Pongkemon01/ServoCoordinator/Software/nuttx/Documentation/NuttX320.png

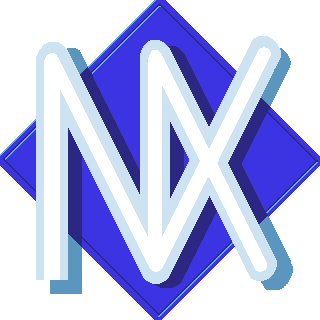
Software/nuttx/Documentation/NuttX320.png
