Pongkemon01/ServoCoordinator/Software/nuttx/Documentation/NuttXScreenShot.jpg

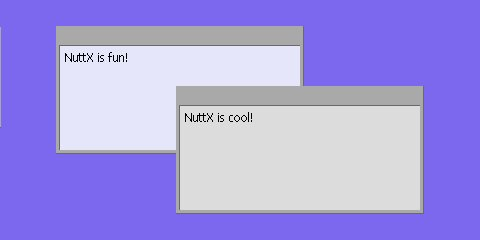
Software/nuttx/Documentation/NuttXScreenShot.jpg
