Pongkemon01/ServoCoordinator/Software/nuttx/Documentation/NXOrganization.gif

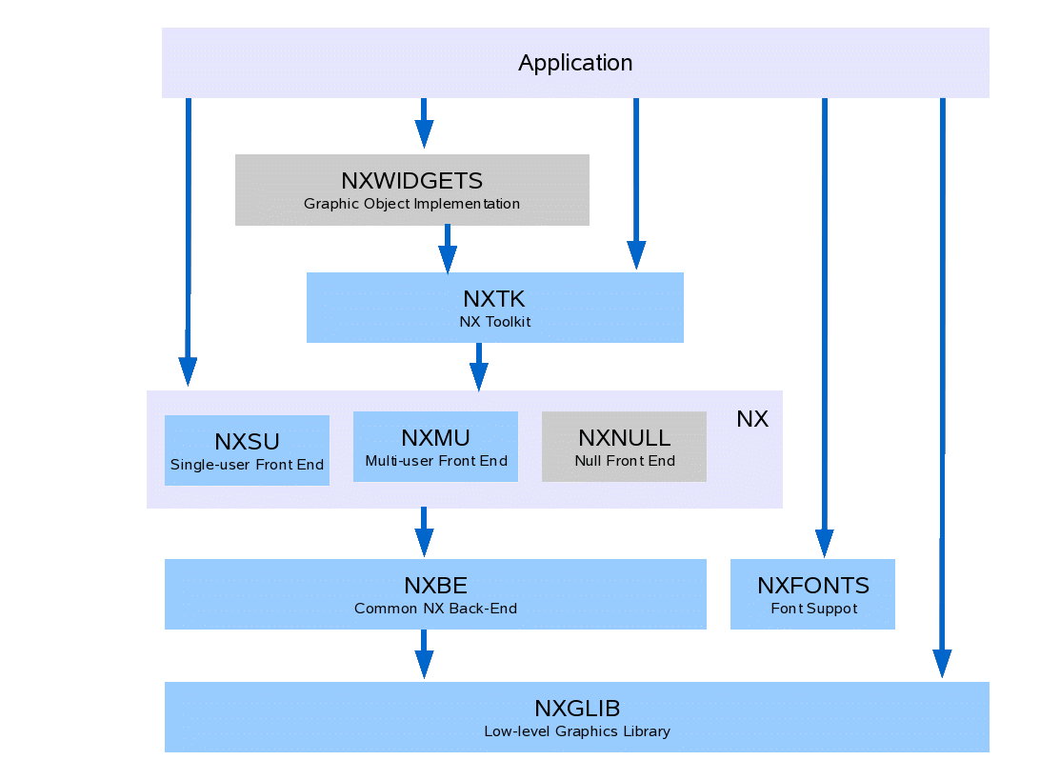
Software/nuttx/Documentation/NXOrganization.gif
