Pongkemon01/ServoCoordinator/Software/nuttx/Documentation/pm.png

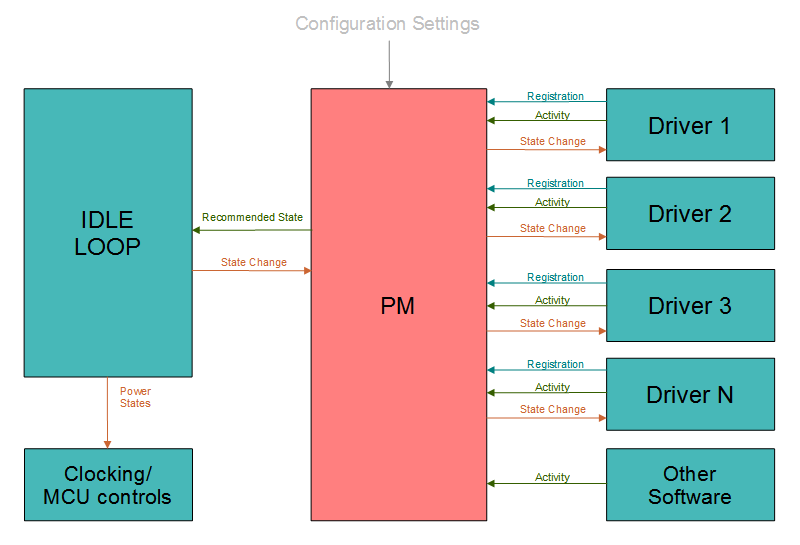
Software/nuttx/Documentation/pm.png
