Pongkemon01/ServoCoordinator/Software/apps/graphics/nxwidgets/UnitTests/CButton/cbutton-pushed.png

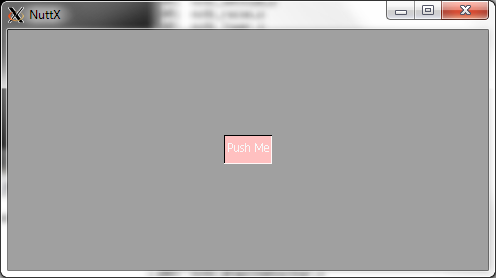
Software/apps/graphics/nxwidgets/UnitTests/CButton/cbutton-pushed.png
