Pongkemon01/ServoCoordinator/Software/apps/graphics/nxwidgets/UnitTests/CButton/cbutton-released.png

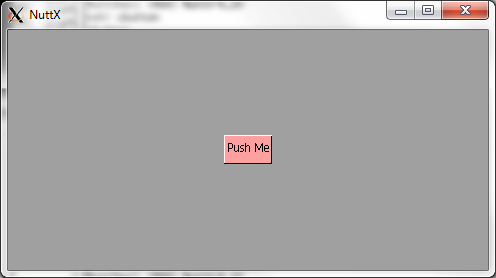
Software/apps/graphics/nxwidgets/UnitTests/CButton/cbutton-released.png
