Pongkemon01/ServoCoordinator/Software/apps/graphics/nxwidgets/UnitTests/CButtonArray/cbuttonarray.png

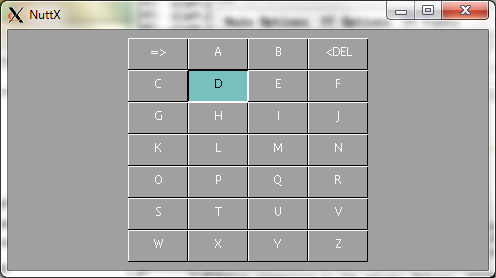
Software/apps/graphics/nxwidgets/UnitTests/CButtonArray/cbuttonarray.png
