Pongkemon01/ServoCoordinator/Software/apps/graphics/nxwidgets/UnitTests/CCheckBox/ccheckbox.png

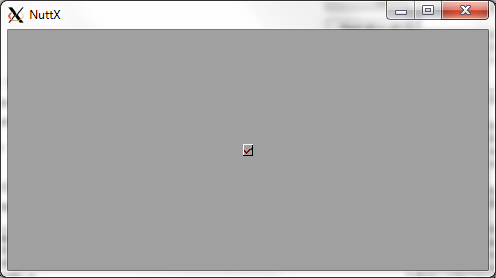
Software/apps/graphics/nxwidgets/UnitTests/CCheckBox/ccheckbox.png
