Pongkemon01/ServoCoordinator/Software/apps/graphics/nxwidgets/UnitTests/CLabel/clabel.png

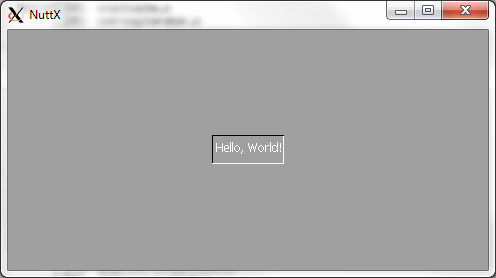
Software/apps/graphics/nxwidgets/UnitTests/CLabel/clabel.png
