Pongkemon01/ServoCoordinator/Software/apps/graphics/nxwidgets/UnitTests/CProgressBar/cprogressbar.png

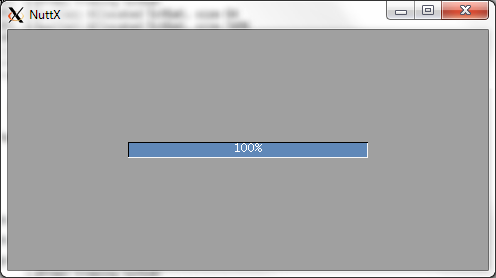
Software/apps/graphics/nxwidgets/UnitTests/CProgressBar/cprogressbar.png
