Pongkemon01/ServoCoordinator/Software/apps/graphics/nxwidgets/UnitTests/CRadioButton/cradiobutton.png

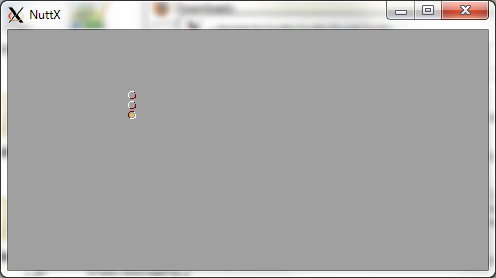
Software/apps/graphics/nxwidgets/UnitTests/CRadioButton/cradiobutton.png
