Pongkemon01/ServoCoordinator/Software/apps/graphics/nxwidgets/UnitTests/CScrollbarHorizontal/cscrollbarhorizontal.png

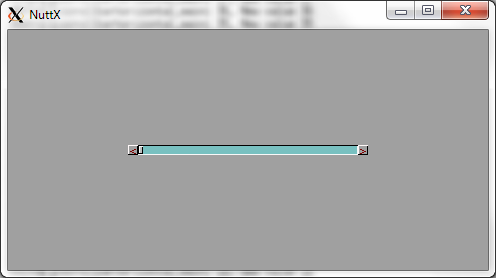
Software/apps/graphics/nxwidgets/UnitTests/CScrollbarHorizontal/cscrollbarhorizontal.png
