Pongkemon01/ServoCoordinator/Software/apps/graphics/nxwidgets/UnitTests/CScrollbarVertical/cscrollbarvertical.png

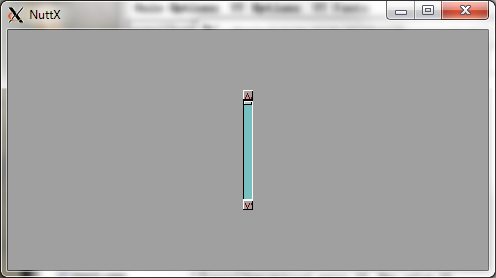
Software/apps/graphics/nxwidgets/UnitTests/CScrollbarVertical/cscrollbarvertical.png
