Pongkemon01/ServoCoordinator/Software/apps/graphics/nxwidgets/UnitTests/CSliderHorizonal/csliderhorizontal.png

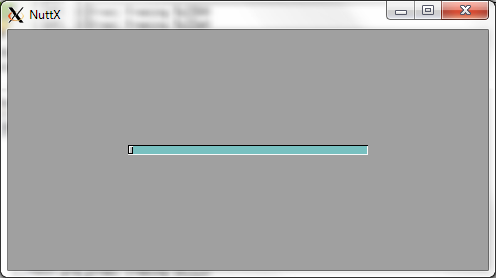
Software/apps/graphics/nxwidgets/UnitTests/CSliderHorizonal/csliderhorizontal.png
