Pongkemon01/ServoCoordinator/Software/apps/graphics/nxwidgets/UnitTests/CSliderVertical/cslidervertical.png

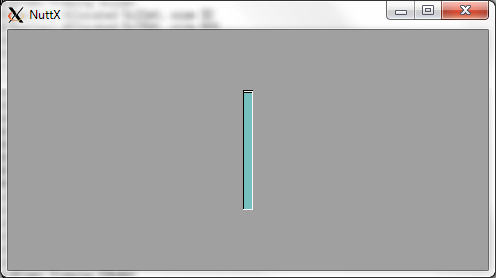
Software/apps/graphics/nxwidgets/UnitTests/CSliderVertical/cslidervertical.png
