Pongkemon01/ServoCoordinator/Software/apps/graphics/nxwidgets/UnitTests/CTextBox/ctextbox.png

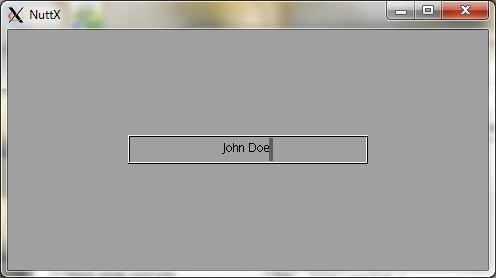
Software/apps/graphics/nxwidgets/UnitTests/CTextBox/ctextbox.png
