Pongkemon01/ServoCoordinator/Software/nuttx/arch/arm/src/kl/kl_gpio.h

/****************************************************************************
 * arch/arm/src/kl/kl_gpio.h
 *
 *   Copyright (C) 2013 Gregory Nutt. All rights reserved.
 *   Author: Gregory Nutt <gnutt@nuttx.org>
 *
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
 * 1. Redistributions of source code must retain the above copyright
 *    notice, this list of conditions and the following disclaimer.
 * 2. Redistributions in binary form must reproduce the above copyright
 *    notice, this list of conditions and the following disclaimer in
 *    the documentation and/or other materials provided with the
 *    distribution.
 * 3. Neither the name NuttX nor the names of its contributors may be
 *    used to endorse or promote products derived from this software
 *    without specific prior written permission.
 *
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
 ****************************************************************************/

#ifndef __ARCH_ARM_SRC_KL_KINETIS_GPIO_H
#define __ARCH_ARM_SRC_KL_KINETIS_GPIO_H

/****************************************************************************
 * Included Files
 ****************************************************************************/

#include <nuttx/config.h>

#include <stdbool.h>

#include <nuttx/irq.h>

#include "kl_config.h"
#include "hardware/kl_gpio.h"
#include "hardware/kl_port.h"

/****************************************************************************
 * Pre-processor Declarations
 ****************************************************************************/
/* Bit-encoded input to kl_pinconfig() *****************************************/
/* General form (32-bits, only 22 bits are unused in the encoding):
 *
 * oooo mmmv iiii ifd- ---- -ppp ---b bbbb
 */

/* Bits 25-31: 7 bits are used to encode the basic pin configuration:
 *
 * oooo mmm- ---- ---- ---- ---- ---- ----
 * |    `--- mmm: mode
 * `------- oooo: options (may be combined)
 */

#define _PIN_MODE_SHIFT        (25)                    /* Bits 25-27: Pin mode */
#define _PIN_MODE_MASK         (7 << _PIN_MODE_SHIFT)
#define _PIN_OPTIONS_SHIFT     (28)                    /* Bits 28-31: Pin mode options */
#define _PIN_OPTIONS_MASK      (15 << _PIN_OPTIONS_SHIFT)

/* Port Modes */

#define PIN_MODE_ANALOG        (0)                     /* 000 Pin Disabled (Analog) */
#define PIN_MODE_GPIO          (1)                     /* 001 Alternative 1 (GPIO) */
#define PIN_MODE_ALT2          (2)                     /* 010 Alternative 2 */
#define PIN_MODE_ALT3          (3)                     /* 011 Alternative 3 */
#define PIN_MODE_ALT4          (4)                     /* 100 Alternative 4 */
#define PIN_MODE_ALT5          (5)                     /* 101 Alternative 5 */
#define PIN_MODE_ALT6          (6)                     /* 110 Alternative 6 */
#define PIN_MODE_ALT7          (7)                     /* 111 Alternative 7 */

#define _PIN_MODE_ANALOG       (0 << _PIN_MODE_SHIFT)  /* 000 Pin Disabled (Analog) */
#define _PIN_MODE_GPIO         (1 << _PIN_MODE_SHIFT)  /* 001 Alternative 1 (GPIO) */
#define _PIN_MODE_ALT2         (2 << _PIN_MODE_SHIFT)  /* 010 Alternative 2 */
#define _PIN_MODE_ALT3         (3 << _PIN_MODE_SHIFT)  /* 011 Alternative 3 */
#define _PIN_MODE_ALT4         (4 << _PIN_MODE_SHIFT)  /* 100 Alternative 4 */
#define _PIN_MODE_ALT5         (5 << _PIN_MODE_SHIFT)  /* 101 Alternative 5 */
#define _PIN_MODE_ALT6         (6 << _PIN_MODE_SHIFT)  /* 110 Alternative 6 */
#define _PIN_MODE_ALT7         (7 << _PIN_MODE_SHIFT)  /* 111 Alternative 7 */

/* Options for all digital modes (Alternatives 1-7).  None of the digital
 * options apply if the analog mode is selected.
 */

#define _PIN_IO_MASK           (1 << _PIN_OPTIONS_SHIFT) /* xxx1 Digital input/output mask */
#define _PIN_INPUT             (0 << _PIN_OPTIONS_SHIFT) /* xxx0 Digital input */
#define _PIN_OUTPUT            (1 << _PIN_OPTIONS_SHIFT) /* xxx1 Digital output */

#define _PIN_INPUT_PULLMASK    (7 << _PIN_OPTIONS_SHIFT) /* x111 Mask for pull-up or -down bits */
#define _PIN_INPUT_PULLDOWN    (2 << _PIN_OPTIONS_SHIFT) /* x010 Input with internal pull-down resistor */
#define _PIN_INPUT_PULLUP      (6 << _PIN_OPTIONS_SHIFT) /* x110 Input with internal pull-up resistor */

#define _PIN_OUTPUT_SLEW_MASK  (3 << _PIN_OPTIONS_SHIFT) /* xx11 Mask to test for slow slew rate */
#define _PIN_OUTPUT_FAST       (1 << _PIN_OPTIONS_SHIFT) /* xx01 Output with fast slew rate */
#define _PIN_OUTPUT_SLOW       (3 << _PIN_OPTIONS_SHIFT) /* xx11 Output with slow slew rate */
#define _PIN_OUTPUT_OD_MASK    (5 << _PIN_OPTIONS_SHIFT) /* x1x1 Mask to test for open drain */
#define _PIN_OUTPUT_OPENDRAIN  (5 << _PIN_OPTIONS_SHIFT) /* x1x1 Output with open drain enabled */
#define _PIN_OUTPUT_DRIVE_MASK (9 << _PIN_OPTIONS_SHIFT) /* 1xx1 Mask to test for high drive strengh */
#define _PIN_OUTPUT_LOWDRIVE   (1 << _PIN_OPTIONS_SHIFT) /* 0xx1 Output with low drive strength */
#define _PIN_OUTPUT_HIGHDRIVE  (9 << _PIN_OPTIONS_SHIFT) /* 1xx1 Output with high drive strength */

/* End-user pin modes and configurations.  Notes:  (1) None of the digital options
 * are available for the analog mode, (2) digital settings may be combined (OR'ed)
 * provided that input-only and output-only options are not intermixed.
 */

#define PIN_ANALOG             _PIN_MODE_ANALOG

#define GPIO_INPUT             (_PIN_MODE_GPIO | _PIN_INPUT)
#define GPIO_PULLDOWN          (_PIN_MODE_GPIO | _PIN_INPUT_PULLDOWN)
#define GPIO_PULLUP            (_PIN_MODE_GPIO | _PIN_INPUT_PULLUP)
#define GPIO_OUTPUT            (_PIN_MODE_GPIO | _PIN_OUTPUT)
#define GPIO_FAST              (_PIN_MODE_GPIO | _PIN_OUTPUT_FAST)
#define GPIO_SLOW              (_PIN_MODE_GPIO | _PIN_OUTPUT_SLOW)
#define GPIO_OPENDRAIN         (_PIN_MODE_GPIO | _PIN_OUTPUT_LOWDRIVE)
#define GPIO_LOWDRIVE          (_PIN_MODE_GPIO | _PIN_OUTPUT_OPENDRAIN)
#define GPIO_HIGHDRIVE         (_PIN_MODE_GPIO | _PIN_OUTPUT_HIGHDRIVE)

#define PIN_ALT2               _PIN_MODE_ALT2
#define PIN_ALT2_INPUT         (_PIN_MODE_ALT2 | _PIN_INPUT)
#define PIN_ALT2_PULLDOWN      (_PIN_MODE_ALT2 | _PIN_INPUT_PULLDOWN)
#define PIN_ALT2_PULLUP        (_PIN_MODE_ALT2 | _PIN_INPUT_PULLUP)
#define PIN_ALT2_OUTPUT        (_PIN_MODE_ALT2 | _PIN_OUTPUT)
#define PIN_ALT2_FAST          (_PIN_MODE_ALT2 | _PIN_OUTPUT_FAST)
#define PIN_ALT2_SLOW          (_PIN_MODE_ALT2 | _PIN_OUTPUT_SLOW)
#define PIN_ALT2_OPENDRAIN     (_PIN_MODE_ALT2 | _PIN_OUTPUT_LOWDRIVE)
#define PIN_ALT2_LOWDRIVE      (_PIN_MODE_ALT2 | _PIN_OUTPUT_OPENDRAIN)
#define PIN_ALT2_HIGHDRIVE     (_PIN_MODE_ALT2 | _PIN_OUTPUT_HIGHDRIVE)

#define PIN_ALT3               _PIN_MODE_ALT3
#define PIN_ALT3_INPUT         (_PIN_MODE_ALT3 | _PIN_INPUT)
#define PIN_ALT3_PULLDOWN      (_PIN_MODE_ALT3 | _PIN_INPUT_PULLDOWN)
#define PIN_ALT3_PULLUP        (_PIN_MODE_ALT3 | _PIN_INPUT_PULLUP)
#define PIN_ALT3_OUTPUT        (_PIN_MODE_ALT3 | _PIN_OUTPUT)
#define PIN_ALT3_FAST          (_PIN_MODE_ALT3 | _PIN_OUTPUT_FAST)
#define PIN_ALT3_SLOW          (_PIN_MODE_ALT3 | _PIN_OUTPUT_SLOW)
#define PIN_ALT3_OPENDRAIN     (_PIN_MODE_ALT3 | _PIN_OUTPUT_LOWDRIVE)
#define PIN_ALT3_LOWDRIVE      (_PIN_MODE_ALT3 | _PIN_OUTPUT_OPENDRAIN)
#define PIN_ALT3_HIGHDRIVE     (_PIN_MODE_ALT3 | _PIN_OUTPUT_HIGHDRIVE)

#define PIN_ALT4               _PIN_MODE_ALT4
#define PIN_ALT4_INPUT         (_PIN_MODE_ALT4 | _PIN_INPUT)
#define PIN_ALT4_PULLDOWN      (_PIN_MODE_ALT4 | _PIN_INPUT_PULLDOWN)
#define PIN_ALT4_PULLUP        (_PIN_MODE_ALT4 | _PIN_INPUT_PULLUP)
#define PIN_ALT4_OUTPUT        (_PIN_MODE_ALT4 | _PIN_OUTPUT)
#define PIN_ALT4_FAST          (_PIN_MODE_ALT4 | _PIN_OUTPUT_FAST)
#define PIN_ALT4_SLOW          (_PIN_MODE_ALT4 | _PIN_OUTPUT_SLOW)
#define PIN_ALT4_OPENDRAIN     (_PIN_MODE_ALT4 | _PIN_OUTPUT_LOWDRIVE)
#define PIN_ALT4_LOWDRIVE      (_PIN_MODE_ALT4 | _PIN_OUTPUT_OPENDRAIN)
#define PIN_ALT4_HIGHDRIVE     (_PIN_MODE_ALT4 | _PIN_OUTPUT_HIGHDRIVE)

#define PIN_ALT5               _PIN_MODE_ALT5
#define PIN_ALT5_INPUT         (_PIN_MODE_ALT5 | _PIN_INPUT)
#define PIN_ALT5_PULLDOWN      (_PIN_MODE_ALT5 | _PIN_INPUT_PULLDOWN)
#define PIN_ALT5_PULLUP        (_PIN_MODE_ALT5 | _PIN_INPUT_PULLUP)
#define PIN_ALT5_OUTPUT        (_PIN_MODE_ALT5 | _PIN_OUTPUT)
#define PIN_ALT5_FAST          (_PIN_MODE_ALT5 | _PIN_OUTPUT_FAST)
#define PIN_ALT5_SLOW          (_PIN_MODE_ALT5 | _PIN_OUTPUT_SLOW)
#define PIN_ALT5_OPENDRAIN     (_PIN_MODE_ALT5 | _PIN_OUTPUT_LOWDRIVE)
#define PIN_ALT5_LOWDRIVE      (_PIN_MODE_ALT5 | _PIN_OUTPUT_OPENDRAIN)
#define PIN_ALT5_HIGHDRIVE     (_PIN_MODE_ALT5 | _PIN_OUTPUT_HIGHDRIVE)

#define PIN_ALT6               _PIN_MODE_ALT6
#define PIN_ALT6_INPUT         (_PIN_MODE_ALT6 | _PIN_INPUT)
#define PIN_ALT6_PULLDOWN      (_PIN_MODE_ALT6 | _PIN_INPUT_PULLDOWN)
#define PIN_ALT6_PULLUP        (_PIN_MODE_ALT6 | _PIN_INPUT_PULLUP)
#define PIN_ALT6_OUTPUT        (_PIN_MODE_ALT6 | _PIN_OUTPUT)
#define PIN_ALT6_FAST          (_PIN_MODE_ALT6 | _PIN_OUTPUT_FAST)
#define PIN_ALT6_SLOW          (_PIN_MODE_ALT6 | _PIN_OUTPUT_SLOW)
#define PIN_ALT6_OPENDRAIN     (_PIN_MODE_ALT6 | _PIN_OUTPUT_LOWDRIVE)
#define PIN_ALT6_LOWDRIVE      (_PIN_MODE_ALT6 | _PIN_OUTPUT_OPENDRAIN)
#define PIN_ALT6_HIGHDRIVE     (_PIN_MODE_ALT6 | _PIN_OUTPUT_HIGHDRIVE)

#define PIN_ALT7               _PIN_MODE_ALT7
#define PIN_ALT7_INPUT         (_PIN_MODE_ALT7 | _PIN_INPUT)
#define PIN_ALT7_PULLDOWN      (_PIN_MODE_ALT7 | _PIN_INPUT_PULLDOWN)
#define PIN_ALT7_PULLUP        (_PIN_MODE_ALT7 | _PIN_INPUT_PULLUP)
#define PIN_ALT7_OUTPUT        (_PIN_MODE_ALT7 | _PIN_OUTPUT)
#define PIN_ALT7_FAST          (_PIN_MODE_ALT7 | _PIN_OUTPUT_FAST)
#define PIN_ALT7_SLOW          (_PIN_MODE_ALT7 | _PIN_OUTPUT_SLOW)
#define PIN_ALT7_OPENDRAIN     (_PIN_MODE_ALT7 | _PIN_OUTPUT_LOWDRIVE)
#define PIN_ALT7_LOWDRIVE      (_PIN_MODE_ALT7 | _PIN_OUTPUT_OPENDRAIN)
#define PIN_ALT7_HIGHDRIVE     (_PIN_MODE_ALT7 | _PIN_OUTPUT_HIGHDRIVE)

/* The initial value for GPIO (Alternative 1 outputs):
 *
 * ---- ---v ---- ---- ---- ---- ---- ----
 *
 * Passive Filter and digital filter enable are valid in all digital pin
 * muxing modes.
 */

#define GPIO_OUTPUT_ONE        (1 << 24)  /* Bit 24: 1:Initial output value=1 */
#define GPIO_OUTPUT_ZER0       (0)        /* Bit 24: 0:Initial output value=0 */

/* Five bits are used to incode DMA/interrupt options:
 *
 * ---- ---- iiii i--- ---- ---- ---- ----
 *
 * The pin interrupt configuration is valid in all digital pin muxing modes
 * (restricted to inputs).
 */

#define _PIN_INT_SHIFT         (20)
#define _PIN_INT_MASK          (31 << _PIN_INT_SHIFT)

#define _PIN_INTDMA_MASK       (3 << _PIN_INT_SHIFT)
#define _PIN_INTDMA_NONE       (0 << _PIN_INT_SHIFT)
#define _PIN_DMA               (1 << _PIN_INT_SHIFT)
#define _PIN_INTERRUPT         (2 << _PIN_INT_SHIFT)

#define PIN_DMA_RISING         (5  << _PIN_INT_SHIFT) /* 00101 DMA Request on rising edge */
#define PIN_DMA_FALLING        (9  << _PIN_INT_SHIFT) /* 01001 DMA Request on falling edge */
#define PIN_DMA_BOTH           (13 << _PIN_INT_SHIFT) /* 01101 DMA Request on either edge */
#define PIN_INT_ZERO           (2  << _PIN_INT_SHIFT) /* 00010 Interrupt when logic zero */
#define PIN_INT_RISING         (6  << _PIN_INT_SHIFT) /* 00110 Interrupt on rising edge */
#define PIN_INT_FALLING        (10 << _PIN_INT_SHIFT) /* 01010 Interrupt on falling edge */
#define PIN_INT_BOTH           (14 << _PIN_INT_SHIFT) /* 01110 Interrupt on either edge */
#define PIN_INT_ONE            (18 << _PIN_INT_SHIFT) /* 10010 Interrupt when logic one */

/* Two bits is used to enable the filter options:
 *
 * ---- ---- ---- -fd- ---- ---- ---- ----
 *
 * Passive Filter and digital filter enable are valid in all digital pin
 * muxing modes.
 */

#define PIN_PASV_FILTER        (1 << 18)  /* Bit 18: Enable passive filter */
#define PIN_DIG_FILTER         (1 << 17)  /* Bit 17: Enable digital filter */

/* Three bits are used to define the port number:
 *
 * ---- ---- ---- ---- ---- -ppp ---- ----
 */

#define _PIN_PORT_SHIFT        (8)  /* Bits 8-10: port number */
#define _PIN_PORT_MASK         (7 << _PIN_PORT_SHIFT)

#define PIN_PORTA              (KL_PORTA << _PIN_PORT_SHIFT)
#define PIN_PORTB              (KL_PORTB << _PIN_PORT_SHIFT)
#define PIN_PORTC              (KL_PORTC << _PIN_PORT_SHIFT)
#define PIN_PORTD              (KL_PORTD << _PIN_PORT_SHIFT)
#define PIN_PORTE              (KL_PORTE << _PIN_PORT_SHIFT)

/* Five bits are used to define the pin number:
 *
 * ---- ---- ---- ---- ---- ---- ---b bbbb
 */

#define _PIN_SHIFT             (0)  /* Bits 0-4: port number */
#define _PIN_MASK              (31 << _PIN_SHIFT)

#define PIN(n)                 ((n) << _PIN_SHIFT)
#define PIN0                   (0 << _PIN_SHIFT)
#define PIN1                   (1 << _PIN_SHIFT)
#define PIN2                   (2 << _PIN_SHIFT)
#define PIN3                   (3 << _PIN_SHIFT)
#define PIN4                   (4 << _PIN_SHIFT)
#define PIN5                   (5 << _PIN_SHIFT)
#define PIN6                   (6 << _PIN_SHIFT)
#define PIN7                   (7 << _PIN_SHIFT)
#define PIN8                   (8 << _PIN_SHIFT)
#define PIN9                   (9 << _PIN_SHIFT)
#define PIN10                  (10 << _PIN_SHIFT)
#define PIN11                  (11 << _PIN_SHIFT)
#define PIN12                  (12 << _PIN_SHIFT)
#define PIN13                  (13 << _PIN_SHIFT)
#define PIN14                  (14 << _PIN_SHIFT)
#define PIN15                  (15 << _PIN_SHIFT)
#define PIN16                  (16 << _PIN_SHIFT)
#define PIN17                  (17 << _PIN_SHIFT)
#define PIN18                  (18 << _PIN_SHIFT)
#define PIN19                  (19 << _PIN_SHIFT)
#define PIN20                  (20 << _PIN_SHIFT)
#define PIN21                  (21 << _PIN_SHIFT)
#define PIN22                  (22 << _PIN_SHIFT)
#define PIN23                  (23 << _PIN_SHIFT)
#define PIN24                  (24 << _PIN_SHIFT)
#define PIN25                  (25 << _PIN_SHIFT)
#define PIN26                  (26 << _PIN_SHIFT)
#define PIN27                  (27 << _PIN_SHIFT)
#define PIN28                  (28 << _PIN_SHIFT)
#define PIN29                  (29 << _PIN_SHIFT)
#define PIN30                  (30 << _PIN_SHIFT)
#define PIN31                  (31 << _PIN_SHIFT)

/****************************************************************************
 * Public Types
 ****************************************************************************/

typedef uint32_t gpio_cfgset_t;

/****************************************************************************
 * Public Data
 ****************************************************************************/

#ifndef __ASSEMBLY__

#undef EXTERN
#if defined(__cplusplus)
#define EXTERN extern "C"
extern "C"
{
#else
#define EXTERN extern
#endif

/****************************************************************************
 * Public Function Prototypes
 ****************************************************************************/

/****************************************************************************
 * Name: kl_configgpio
 *
 * Description:
 *   Configure a PIN based on bit-encoded description of the pin.  NOTE that
 *   DMA/interrupts are disabled at the initial PIN configuratin.
 *
 ****************************************************************************/

int kl_configgpio(uint32_t cfgset);

/****************************************************************************
 * Name: kl_gpiowrite
 *
 * Description:
 *   Write one or zero to the selected GPIO pin
 *
 ****************************************************************************/

void kl_gpiowrite(uint32_t pinset, bool value);

/****************************************************************************
 * Name: kl_gpioread
 *
 * Description:
 *   Read one or zero from the selected GPIO pin
 *
 ****************************************************************************/

bool kl_gpioread(uint32_t pinset);

/************************************************************************************
 * Name: kl_gpioirqattach
 *
 * Description:
 *   Attach a pin interrupt handler.  The normal initialization sequence is:
 *
 *   1. Call kl_configgpio() to configure the interrupting pin (pin interrupts
 *      will be disabled.
 *   2. Call kl_gpioirqattach() to attach the pin interrupt handling function.
 *   3. Call kl_gpioirqenable() to enable interrupts on the pin.
 *
 * Input Parameters:
 *  - pinset:  Pin configuration
 *  - pinisr:  Pin interrupt service routine
 *  - pinarg:  The argument that will accompany the pin interrupt
 *
 * Returned Value:
 *   Zero (OK) is returned on success; On any failure, a negated errno value is
 *   returned to indicate the nature of the failure.
 *
 ************************************************************************************/

int kl_gpioirqattach(uint32_t pinset, xcpt_t pinisr, void *pinarg);

/************************************************************************************
 * Name: kl_gpioirqenable
 *
 * Description:
 *   Enable the interrupt for specified pin IRQ
 *
 ************************************************************************************/

#ifdef CONFIG_KL_GPIOIRQ
void kl_gpioirqenable(uint32_t pinset);
#else
#  define kl_gpioirqenable(pinset)
#endif

/************************************************************************************
 * Name: kl_gpioirqdisable
 *
 * Description:
 *   Disable the interrupt for specified pin
 *
 ************************************************************************************/

#ifdef CONFIG_KL_GPIOIRQ
void kl_gpioirqdisable(uint32_t pinset);
#else
#  define kl_gpioirqdisable(pinset)
#endif

#undef EXTERN
#if defined(__cplusplus)
}
#endif
#endif /* __ASSEMBLY__ */
#endif /* __ARCH_ARM_SRC_KL_KINETIS_GPIO_H */
